rrainey/dropkick/images/imu-axes.graffle/image1.png

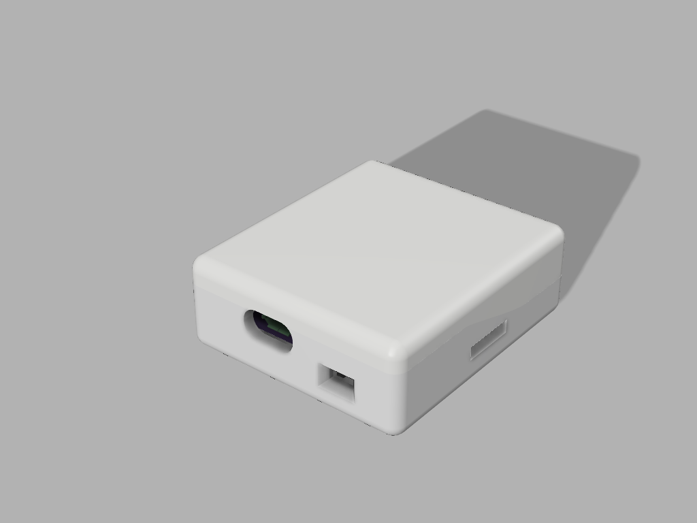
images/imu-axes.graffle/image1.png
